TommyStyrvoky/Realm-card/animations/blizzard/1.bmp

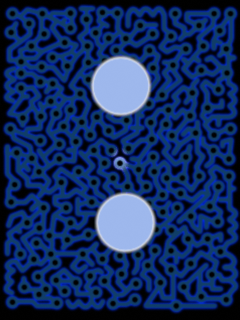
animations/blizzard/1.bmp
