TommyStyrvoky/Realm-card/animations/blizzard/3.bmp

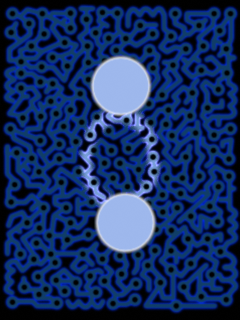
animations/blizzard/3.bmp
