TommyStyrvoky/Realm-card/animations/blizzard/4.bmp

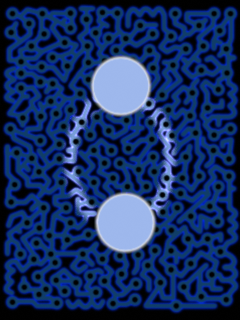
animations/blizzard/4.bmp
