TommyStyrvoky/Realm-card/animations/blizzard/6.bmp

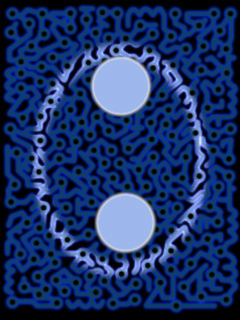
animations/blizzard/6.bmp
