TommyStyrvoky/Realm-card/animations/blizzard/7.bmp

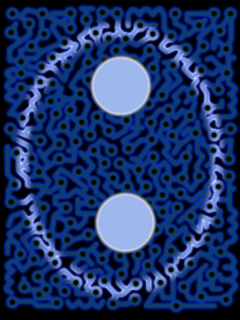
animations/blizzard/7.bmp
