TommyStyrvoky/Realm-card/animations/blizzard/8.bmp

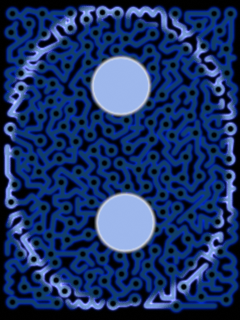
animations/blizzard/8.bmp
