TommyStyrvoky/Realm-card/animations/blizzard/9.bmp

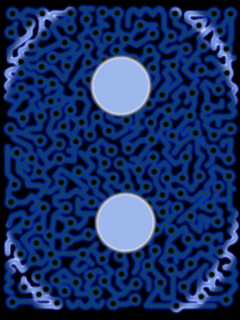
animations/blizzard/9.bmp
