TommyStyrvoky/Realm-card/animations/blizzard/10.bmp

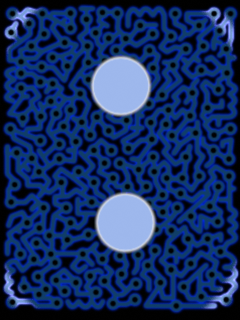
animations/blizzard/10.bmp
