TommyStyrvoky/Realm-card/animations/canyon/2.bmp

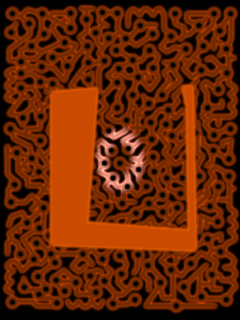
animations/canyon/2.bmp
