TommyStyrvoky/Realm-card/animations/canyon/3.bmp

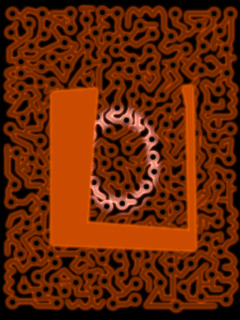
animations/canyon/3.bmp
