TommyStyrvoky/Realm-card/animations/canyon/4.bmp

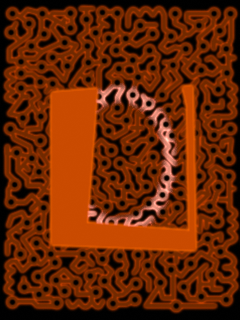
animations/canyon/4.bmp
