TommyStyrvoky/Realm-card/animations/canyon/5.bmp

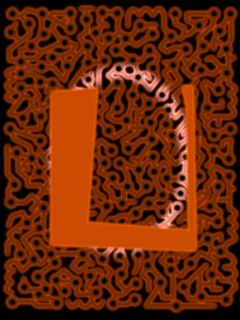
animations/canyon/5.bmp
