TommyStyrvoky/Realm-card/animations/canyon/6.bmp

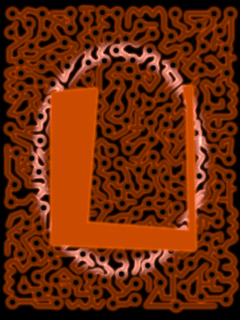
animations/canyon/6.bmp
