TommyStyrvoky/Realm-card/animations/canyon/7.bmp

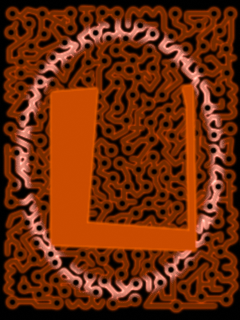
animations/canyon/7.bmp
