TommyStyrvoky/Realm-card/animations/canyon/8.bmp

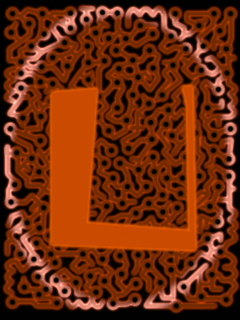
animations/canyon/8.bmp
