TommyStyrvoky/Realm-card/animations/canyon/9.bmp

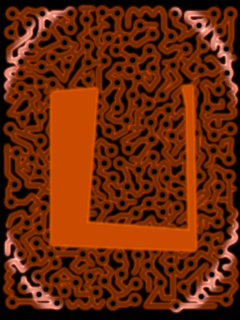
animations/canyon/9.bmp
