TommyStyrvoky/Realm-card/animations/canyon/10.bmp

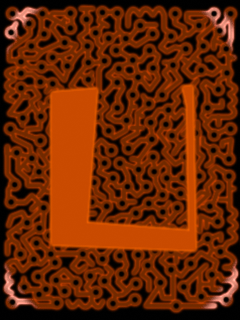
animations/canyon/10.bmp
