TommyStyrvoky/Realm-card/animations/cavern/1.bmp

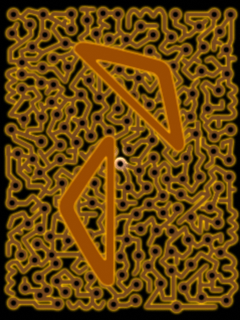
animations/cavern/1.bmp
