TommyStyrvoky/Realm-card/animations/cavern/3.bmp

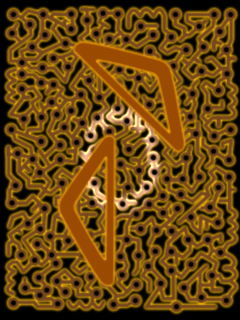
animations/cavern/3.bmp
