TommyStyrvoky/Realm-card/animations/cavern/5.bmp

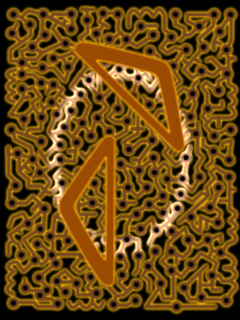
animations/cavern/5.bmp
