TommyStyrvoky/Realm-card/animations/cavern/6.bmp

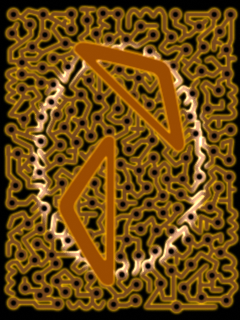
animations/cavern/6.bmp
