TommyStyrvoky/Realm-card/animations/cavern/7.bmp

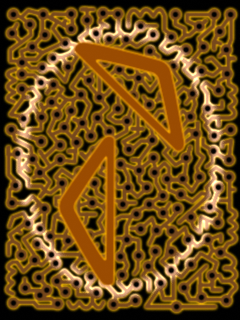
animations/cavern/7.bmp
