TommyStyrvoky/Realm-card/animations/cavern/8.bmp

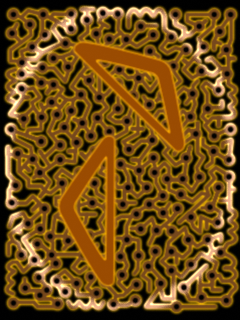
animations/cavern/8.bmp
