TommyStyrvoky/Realm-card/animations/cavern/9.bmp

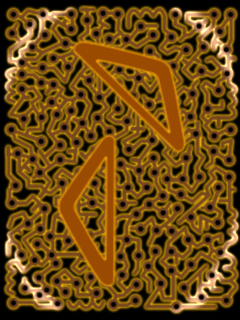
animations/cavern/9.bmp
