TommyStyrvoky/Realm-card/animations/cavern/10.bmp

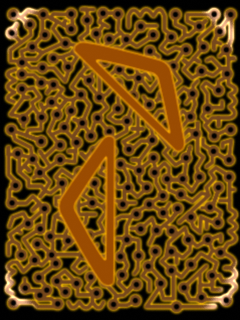
animations/cavern/10.bmp
