TommyStyrvoky/Realm-card/animations/chrome/1.bmp

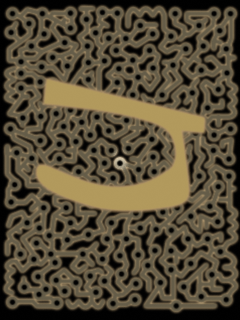
animations/chrome/1.bmp
