TommyStyrvoky/Realm-card/animations/chrome/3.bmp

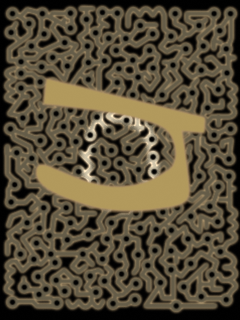
animations/chrome/3.bmp
