TommyStyrvoky/Realm-card/animations/chrome/5.bmp

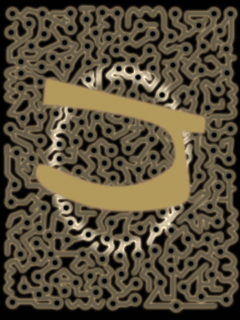
animations/chrome/5.bmp
