TommyStyrvoky/Realm-card/animations/chrome/7.bmp

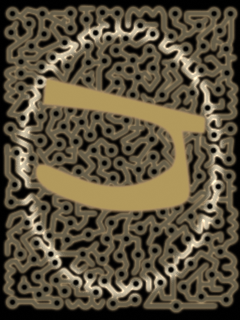
animations/chrome/7.bmp
