TommyStyrvoky/Realm-card/animations/chrome/8.bmp

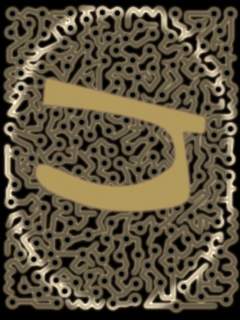
animations/chrome/8.bmp
