TommyStyrvoky/Realm-card/animations/chrome/9.bmp

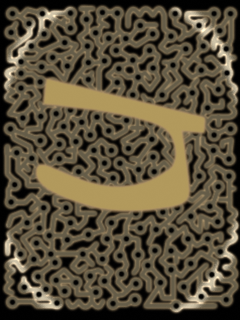
animations/chrome/9.bmp
