TommyStyrvoky/Realm-card/animations/chrome/10.bmp

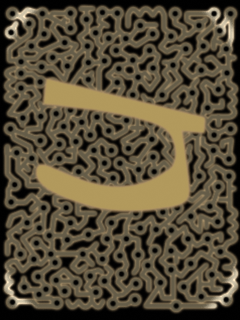
animations/chrome/10.bmp
