TommyStyrvoky/Realm-card/animations/cliffside/1.bmp

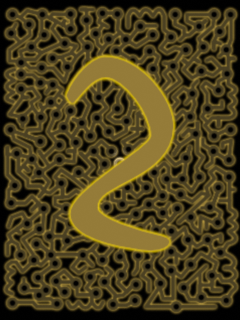
animations/cliffside/1.bmp
