TommyStyrvoky/Realm-card/animations/cliffside/5.bmp

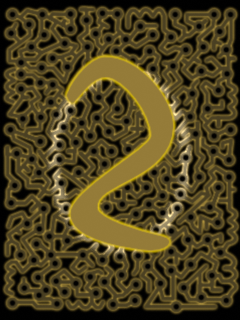
animations/cliffside/5.bmp
