TommyStyrvoky/Realm-card/animations/cliffside/6.bmp

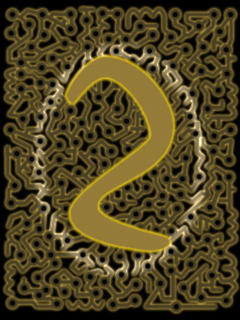
animations/cliffside/6.bmp
