TommyStyrvoky/Realm-card/animations/cliffside/7.bmp

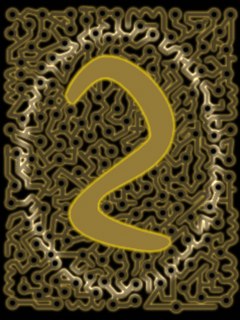
animations/cliffside/7.bmp
