TommyStyrvoky/Realm-card/animations/cosmic/3.bmp

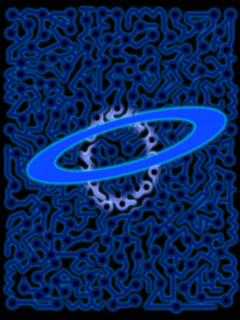
animations/cosmic/3.bmp
