TommyStyrvoky/Realm-card/animations/cosmic/5.bmp

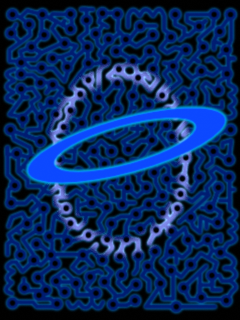
animations/cosmic/5.bmp
