TommyStyrvoky/Realm-card/animations/cosmic/6.bmp

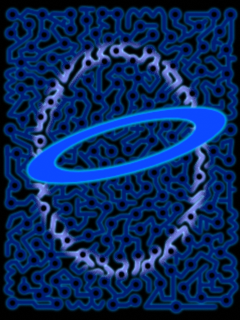
animations/cosmic/6.bmp
