TommyStyrvoky/Realm-card/animations/cosmic/7.bmp

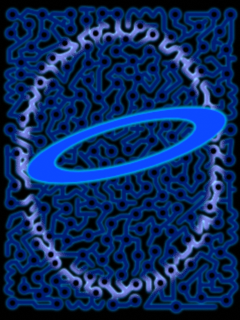
animations/cosmic/7.bmp
