TommyStyrvoky/Realm-card/animations/cosmic/8.bmp

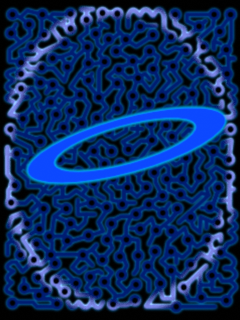
animations/cosmic/8.bmp
