TommyStyrvoky/Realm-card/animations/cosmic/9.bmp

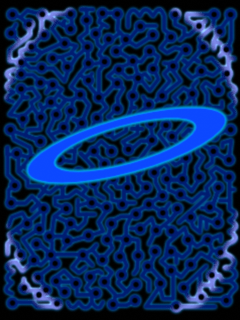
animations/cosmic/9.bmp
