TommyStyrvoky/Realm-card/animations/cybergrid/1.bmp

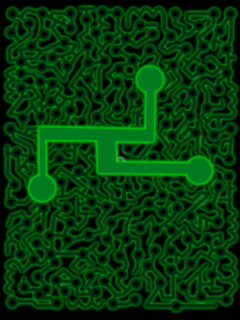
animations/cybergrid/1.bmp
