TommyStyrvoky/Realm-card/animations/cybergrid/4.bmp

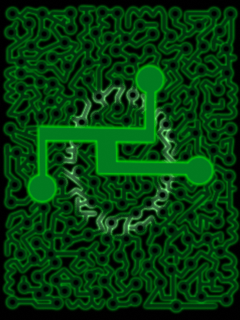
animations/cybergrid/4.bmp
