TommyStyrvoky/Realm-card/animations/cybergrid/5.bmp

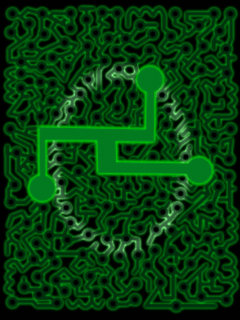
animations/cybergrid/5.bmp
