TommyStyrvoky/Realm-card/animations/cybergrid/6.bmp

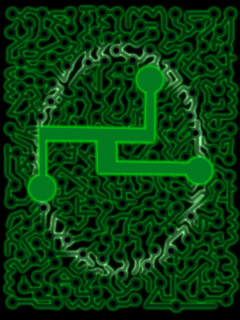
animations/cybergrid/6.bmp
