TommyStyrvoky/Realm-card/animations/cybergrid/7.bmp

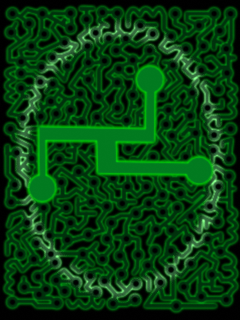
animations/cybergrid/7.bmp
