TommyStyrvoky/Realm-card/animations/cybergrid/8.bmp

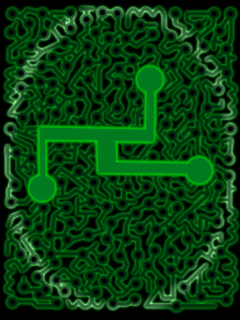
animations/cybergrid/8.bmp
