TommyStyrvoky/Realm-card/animations/cybergrid/9.bmp

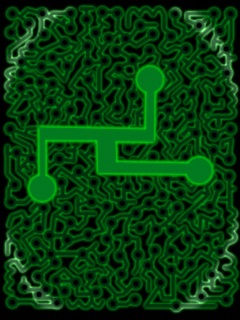
animations/cybergrid/9.bmp
