TommyStyrvoky/Realm-card/animations/cybergrid/10.bmp

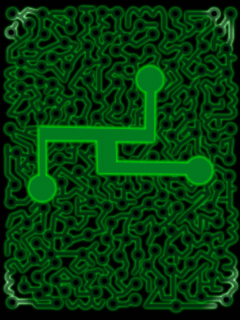
animations/cybergrid/10.bmp
