TommyStyrvoky/Realm-card/animations/desert/2.bmp

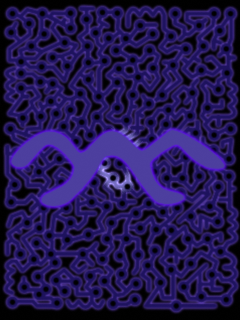
animations/desert/2.bmp
