TommyStyrvoky/Realm-card/animations/desert/4.bmp

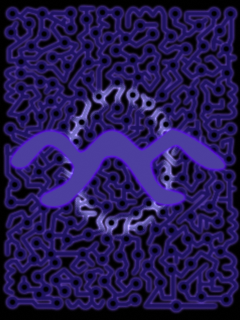
animations/desert/4.bmp
