TommyStyrvoky/Realm-card/animations/desert/5.bmp

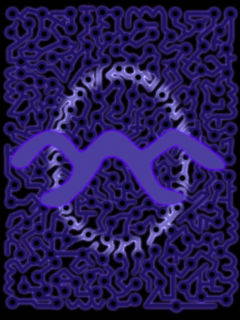
animations/desert/5.bmp
