TommyStyrvoky/Realm-card/animations/desert/7.bmp

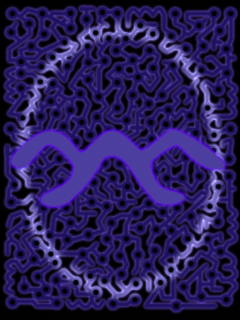
animations/desert/7.bmp
