TommyStyrvoky/Realm-card/animations/desert/8.bmp

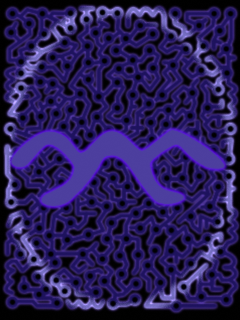
animations/desert/8.bmp
