TommyStyrvoky/Realm-card/animations/desert/9.bmp

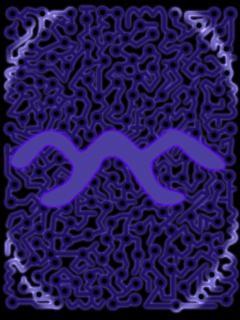
animations/desert/9.bmp
