TommyStyrvoky/Realm-card/animations/desert/10.bmp

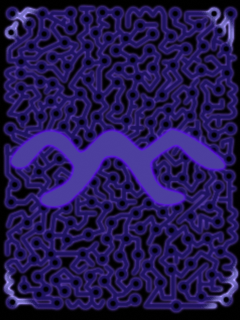
animations/desert/10.bmp
