TommyStyrvoky/Realm-card/animations/fog/1.bmp

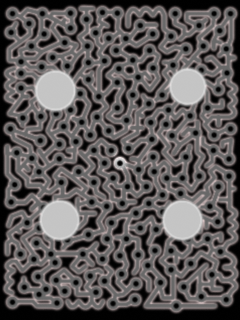
animations/fog/1.bmp
