TommyStyrvoky/Realm-card/animations/fog/3.bmp

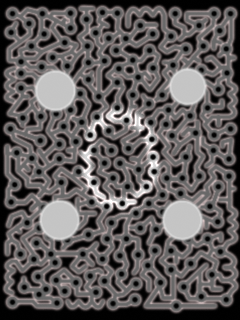
animations/fog/3.bmp
