TommyStyrvoky/Realm-card/animations/fog/4.bmp

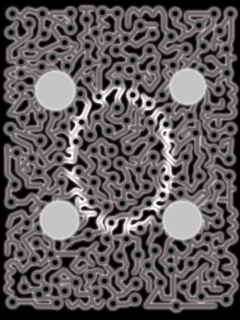
animations/fog/4.bmp
