TommyStyrvoky/Realm-card/animations/fog/5.bmp

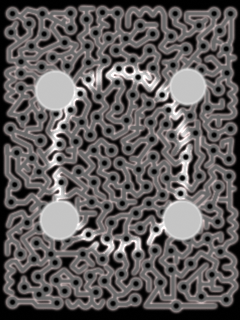
animations/fog/5.bmp
