TommyStyrvoky/Realm-card/animations/fog/6.bmp

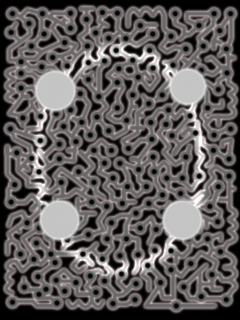
animations/fog/6.bmp
