TommyStyrvoky/Realm-card/animations/fog/7.bmp

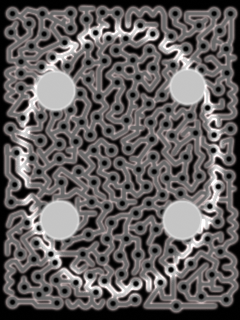
animations/fog/7.bmp
