TommyStyrvoky/Realm-card/animations/fog/8.bmp

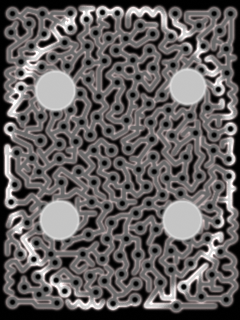
animations/fog/8.bmp
