TommyStyrvoky/Realm-card/animations/fog/9.bmp

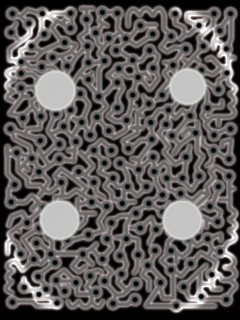
animations/fog/9.bmp
