TommyStyrvoky/Realm-card/animations/fog/10.bmp

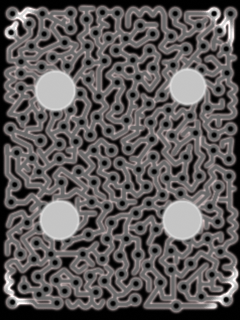
animations/fog/10.bmp
