TommyStyrvoky/Realm-card/animations/forest/1.bmp

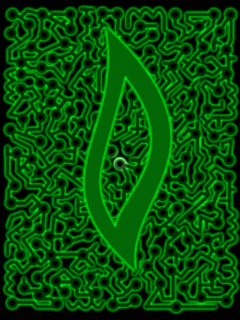
animations/forest/1.bmp
