TommyStyrvoky/Realm-card/animations/forest/4.bmp

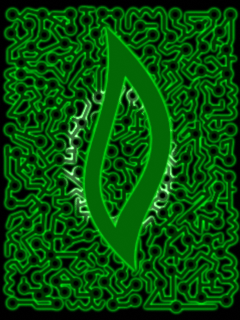
animations/forest/4.bmp
