TommyStyrvoky/Realm-card/animations/forest/6.bmp

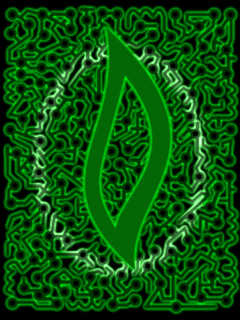
animations/forest/6.bmp
