TommyStyrvoky/Realm-card/animations/forest/7.bmp

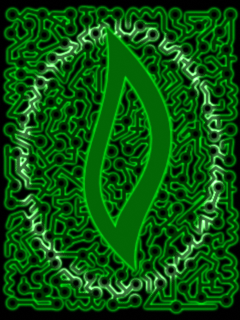
animations/forest/7.bmp
