TommyStyrvoky/Realm-card/animations/forest/8.bmp

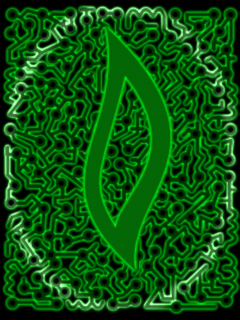
animations/forest/8.bmp
