TommyStyrvoky/Realm-card/animations/forest/9.bmp

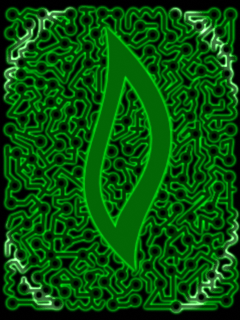
animations/forest/9.bmp
