TommyStyrvoky/Realm-card/animations/glass/2.bmp

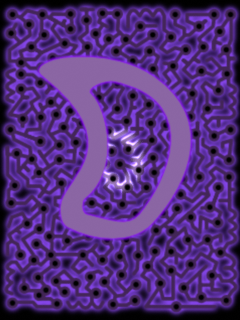
animations/glass/2.bmp
