TommyStyrvoky/Realm-card/animations/glass/3.bmp

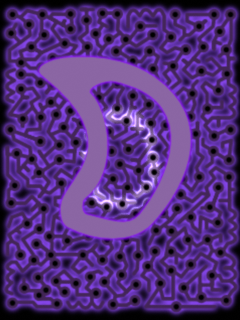
animations/glass/3.bmp
