TommyStyrvoky/Realm-card/animations/glass/4.bmp

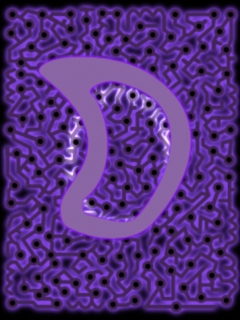
animations/glass/4.bmp
