TommyStyrvoky/Realm-card/animations/glass/5.bmp

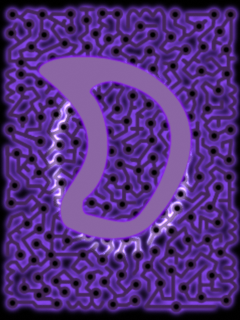
animations/glass/5.bmp
