TommyStyrvoky/Realm-card/animations/glass/6.bmp

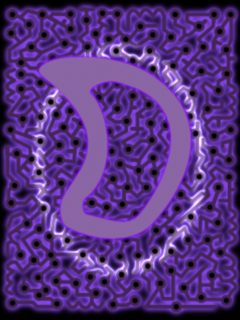
animations/glass/6.bmp
