TommyStyrvoky/Realm-card/animations/glass/7.bmp

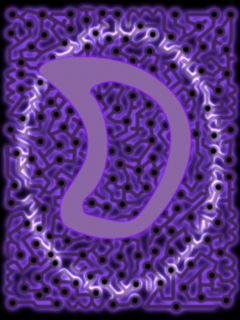
animations/glass/7.bmp
