TommyStyrvoky/Realm-card/animations/glass/8.bmp

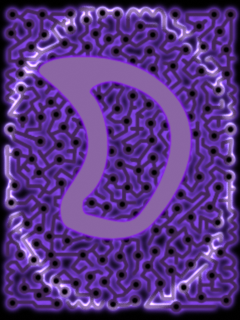
animations/glass/8.bmp
