TommyStyrvoky/Realm-card/animations/glass/9.bmp

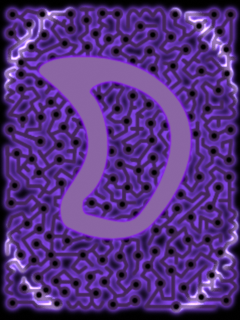
animations/glass/9.bmp
