TommyStyrvoky/Realm-card/animations/glass/10.bmp

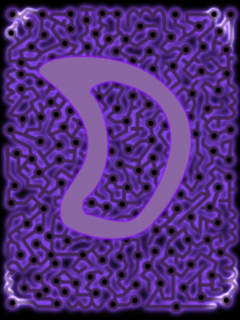
animations/glass/10.bmp
