TommyStyrvoky/Realm-card/animations/ice/1.bmp

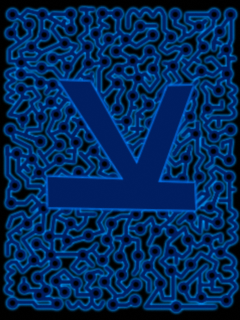
animations/ice/1.bmp
