TommyStyrvoky/Realm-card/animations/ice/3.bmp

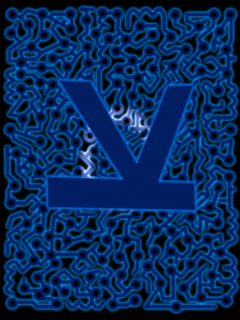
animations/ice/3.bmp
