TommyStyrvoky/Realm-card/animations/ice/4.bmp

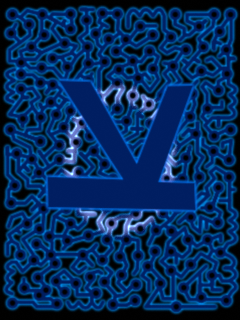
animations/ice/4.bmp
