TommyStyrvoky/Realm-card/animations/ice/5.bmp

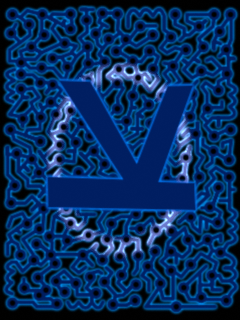
animations/ice/5.bmp
