TommyStyrvoky/Realm-card/animations/ice/8.bmp

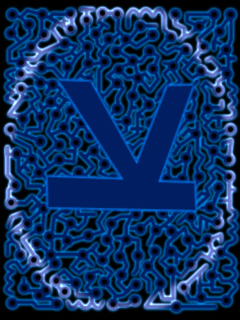
animations/ice/8.bmp
