TommyStyrvoky/Realm-card/animations/ice/9.bmp

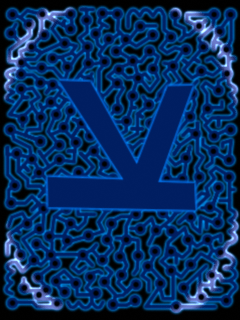
animations/ice/9.bmp
