TommyStyrvoky/Realm-card/animations/ice/10.bmp

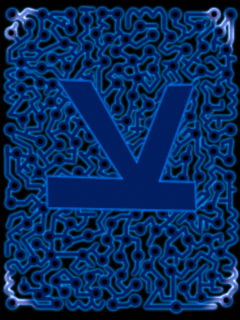
animations/ice/10.bmp
