TommyStyrvoky/Realm-card/animations/junk/1.bmp

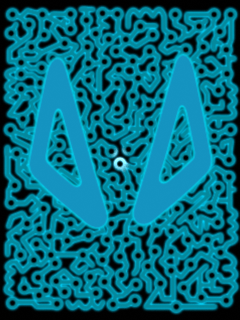
animations/junk/1.bmp
