TommyStyrvoky/Realm-card/animations/junk/2.bmp

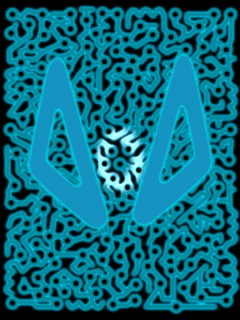
animations/junk/2.bmp
