TommyStyrvoky/Realm-card/animations/junk/3.bmp

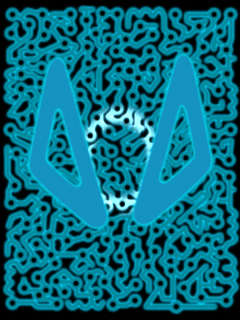
animations/junk/3.bmp
