TommyStyrvoky/Realm-card/animations/junk/6.bmp

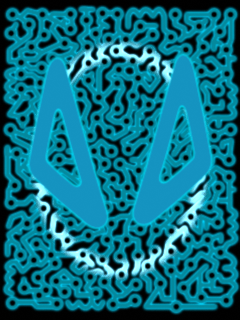
animations/junk/6.bmp
