TommyStyrvoky/Realm-card/animations/junk/7.bmp

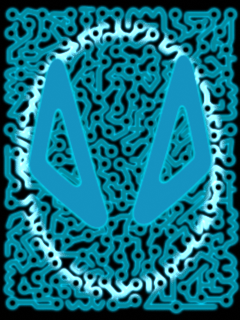
animations/junk/7.bmp
