TommyStyrvoky/Realm-card/animations/junk/8.bmp

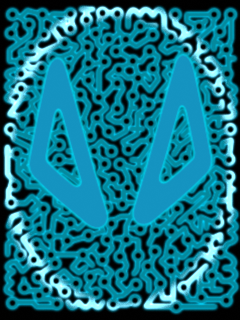
animations/junk/8.bmp
