TommyStyrvoky/Realm-card/animations/junk/9.bmp

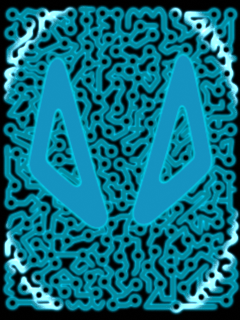
animations/junk/9.bmp
