TommyStyrvoky/Realm-card/animations/junk/10.bmp

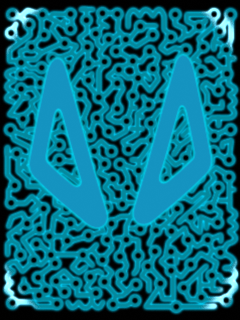
animations/junk/10.bmp
