TommyStyrvoky/Realm-card/animations/labyrinth/1.bmp

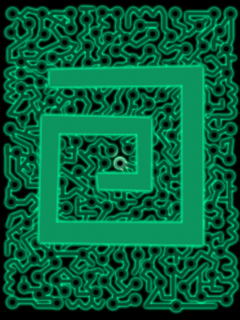
animations/labyrinth/1.bmp
