TommyStyrvoky/Realm-card/animations/labyrinth/3.bmp

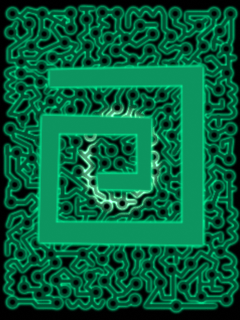
animations/labyrinth/3.bmp
