TommyStyrvoky/Realm-card/animations/labyrinth/4.bmp

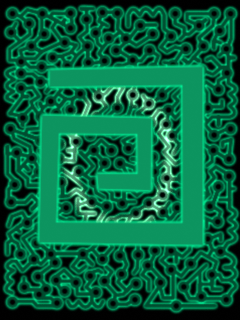
animations/labyrinth/4.bmp
