TommyStyrvoky/Realm-card/animations/labyrinth/6.bmp

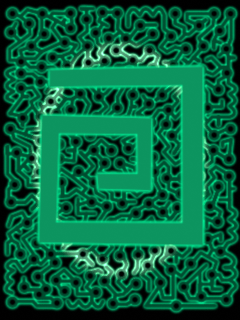
animations/labyrinth/6.bmp
