TommyStyrvoky/Realm-card/animations/labyrinth/7.bmp

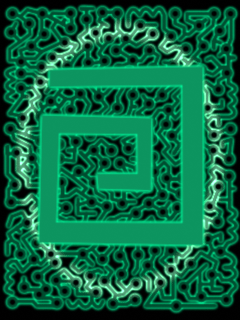
animations/labyrinth/7.bmp
