TommyStyrvoky/Realm-card/animations/labyrinth/8.bmp

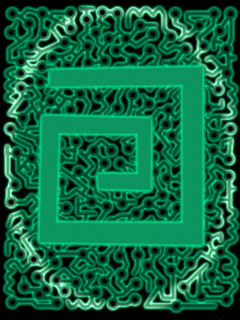
animations/labyrinth/8.bmp
