TommyStyrvoky/Realm-card/animations/labyrinth/9.bmp

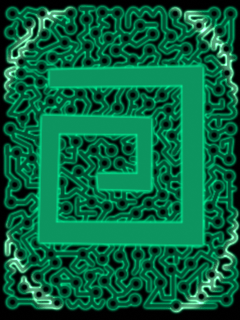
animations/labyrinth/9.bmp
