TommyStyrvoky/Realm-card/animations/labyrinth/10.bmp

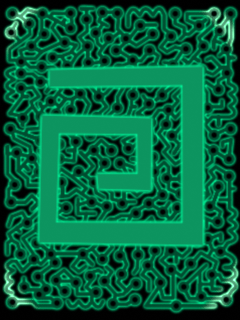
animations/labyrinth/10.bmp
