TommyStyrvoky/Realm-card/animations/lava/1.bmp

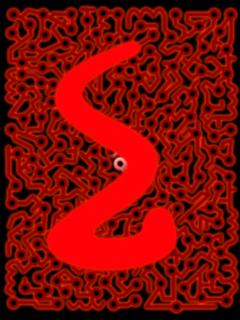
animations/lava/1.bmp
