TommyStyrvoky/Realm-card/animations/lava/3.bmp

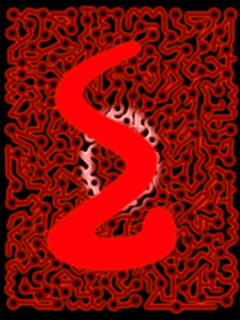
animations/lava/3.bmp
