TommyStyrvoky/Realm-card/animations/lava/5.bmp

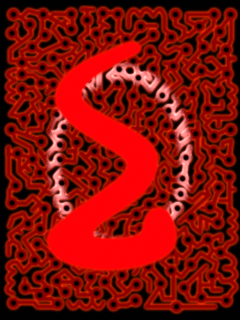
animations/lava/5.bmp
