TommyStyrvoky/Realm-card/animations/lava/6.bmp

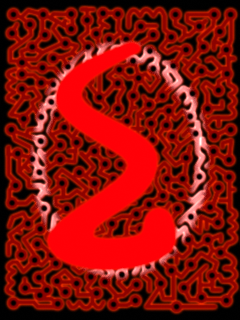
animations/lava/6.bmp
