TommyStyrvoky/Realm-card/animations/lava/7.bmp

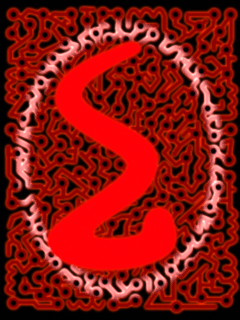
animations/lava/7.bmp
