TommyStyrvoky/Realm-card/animations/lava/8.bmp

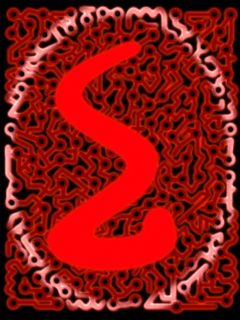
animations/lava/8.bmp
