TommyStyrvoky/Realm-card/animations/lava/9.bmp

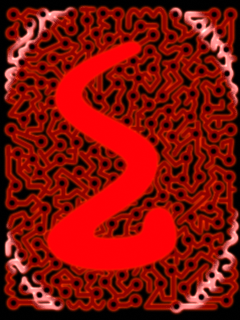
animations/lava/9.bmp
