TommyStyrvoky/Realm-card/animations/lava/10.bmp

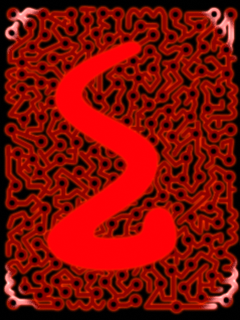
animations/lava/10.bmp
