TommyStyrvoky/Realm-card/animations/metro/1.bmp

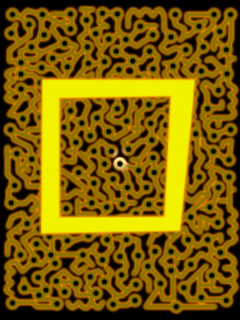
animations/metro/1.bmp
