TommyStyrvoky/Realm-card/animations/metro/3.bmp

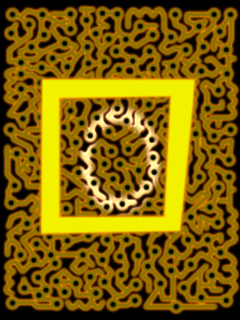
animations/metro/3.bmp
