TommyStyrvoky/Realm-card/animations/metro/4.bmp

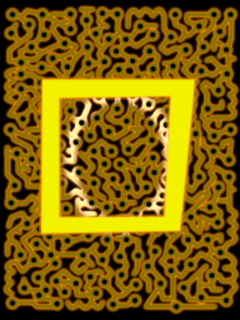
animations/metro/4.bmp
