TommyStyrvoky/Realm-card/animations/metro/5.bmp

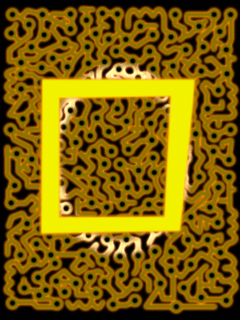
animations/metro/5.bmp
