TommyStyrvoky/Realm-card/animations/metro/7.bmp

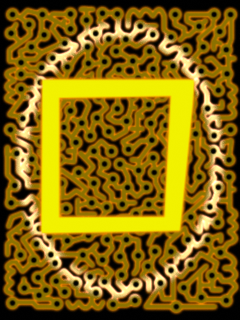
animations/metro/7.bmp
