TommyStyrvoky/Realm-card/animations/metro/8.bmp

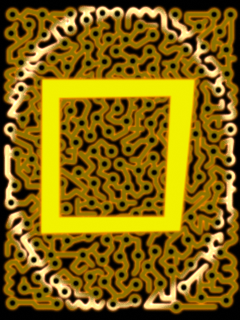
animations/metro/8.bmp
