TommyStyrvoky/Realm-card/animations/metro/9.bmp

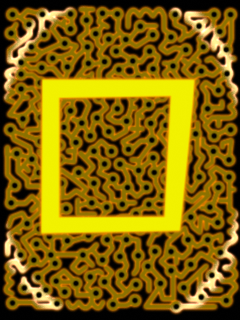
animations/metro/9.bmp
