TommyStyrvoky/Realm-card/animations/metro/10.bmp

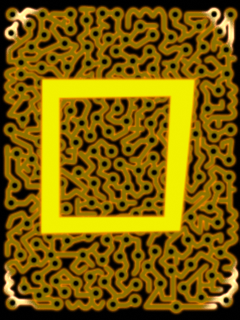
animations/metro/10.bmp
