TommyStyrvoky/Realm-card/animations/micro/1.bmp

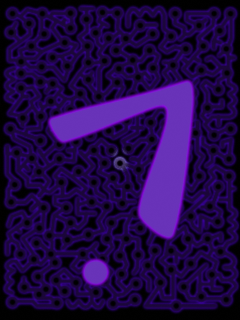
animations/micro/1.bmp
