TommyStyrvoky/Realm-card/animations/micro/3.bmp

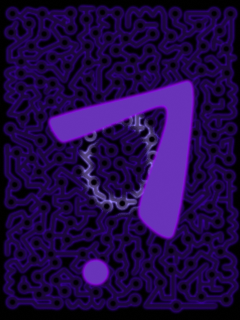
animations/micro/3.bmp
