TommyStyrvoky/Realm-card/animations/micro/4.bmp

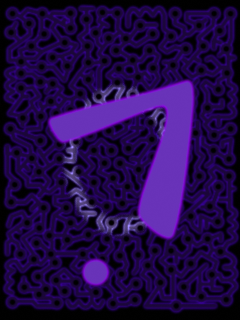
animations/micro/4.bmp
