TommyStyrvoky/Realm-card/animations/micro/6.bmp

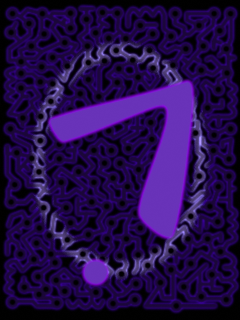
animations/micro/6.bmp
