TommyStyrvoky/Realm-card/animations/micro/7.bmp

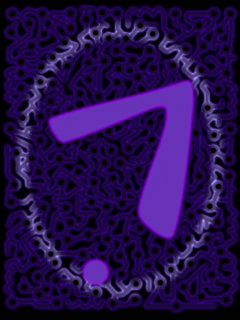
animations/micro/7.bmp
