TommyStyrvoky/Realm-card/animations/micro/8.bmp

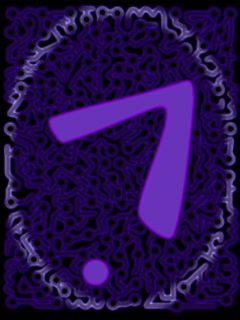
animations/micro/8.bmp
