TommyStyrvoky/Realm-card/animations/micro/9.bmp

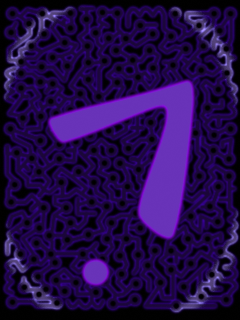
animations/micro/9.bmp
