TommyStyrvoky/Realm-card/animations/micro/10.bmp

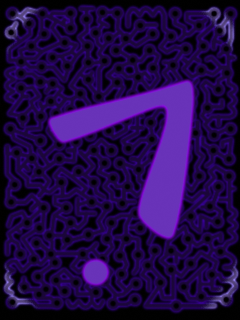
animations/micro/10.bmp
