TommyStyrvoky/Realm-card/animations/monument/1.bmp

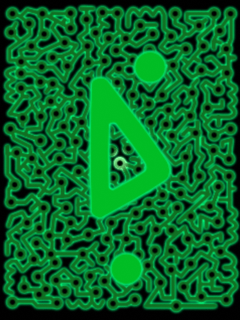
animations/monument/1.bmp
