TommyStyrvoky/Realm-card/animations/monument/4.bmp

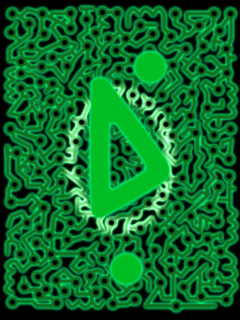
animations/monument/4.bmp
