TommyStyrvoky/Realm-card/animations/monument/6.bmp

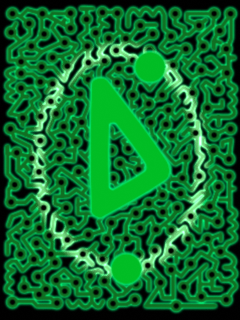
animations/monument/6.bmp
