TommyStyrvoky/Realm-card/animations/monument/7.bmp

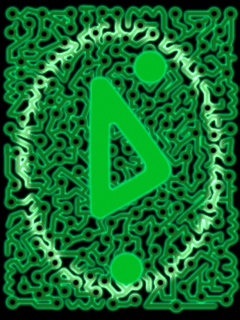
animations/monument/7.bmp
