TommyStyrvoky/Realm-card/animations/neon pipeline/1.bmp

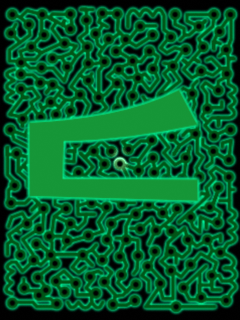
animations/neon pipeline/1.bmp
