TommyStyrvoky/Realm-card/animations/neon pipeline/2.bmp

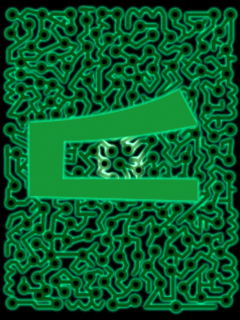
animations/neon pipeline/2.bmp
