TommyStyrvoky/Realm-card/animations/neon pipeline/4.bmp

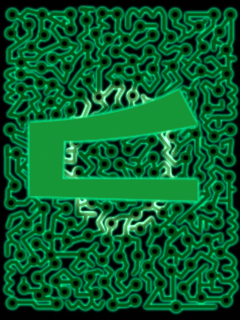
animations/neon pipeline/4.bmp
