TommyStyrvoky/Realm-card/animations/neon pipeline/6.bmp

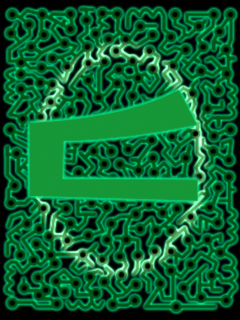
animations/neon pipeline/6.bmp
