TommyStyrvoky/Realm-card/animations/neon pipeline/7.bmp

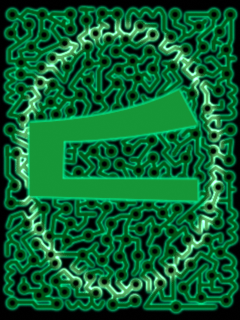
animations/neon pipeline/7.bmp
