TommyStyrvoky/Realm-card/animations/neon pipeline/8.bmp

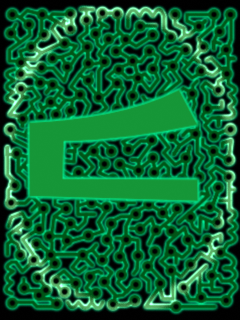
animations/neon pipeline/8.bmp
