TommyStyrvoky/Realm-card/animations/neon pipeline/9.bmp

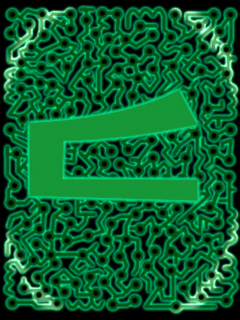
animations/neon pipeline/9.bmp
