TommyStyrvoky/Realm-card/animations/reactor/2.bmp

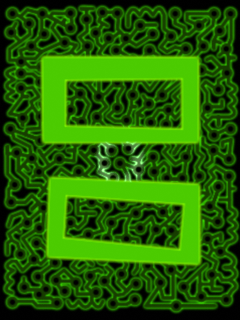
animations/reactor/2.bmp
