TommyStyrvoky/Realm-card/animations/reactor/5.bmp

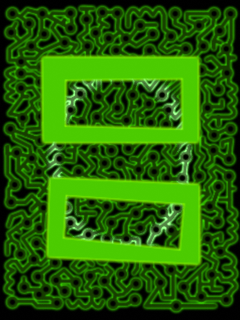
animations/reactor/5.bmp
