TommyStyrvoky/Realm-card/animations/reactor/6.bmp

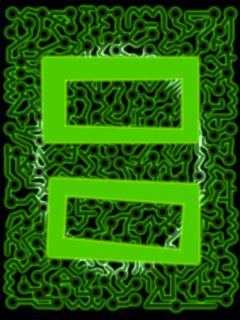
animations/reactor/6.bmp
