TommyStyrvoky/Realm-card/animations/reactor/7.bmp

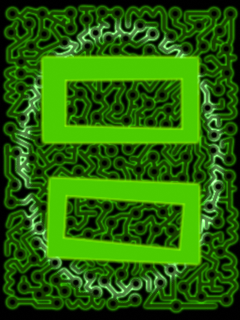
animations/reactor/7.bmp
