TommyStyrvoky/Realm-card/animations/reactor/8.bmp

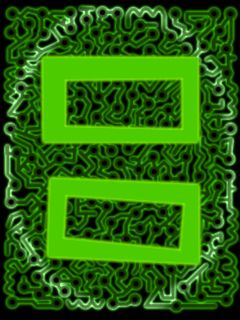
animations/reactor/8.bmp
