TommyStyrvoky/Realm-card/animations/reactor/10.bmp

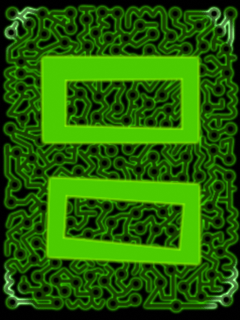
animations/reactor/10.bmp
