TommyStyrvoky/Realm-card/animations/ruins/1.bmp

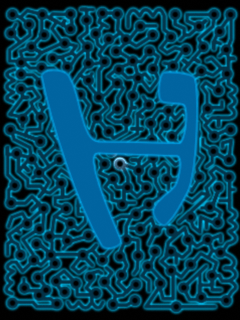
animations/ruins/1.bmp
