TommyStyrvoky/Realm-card/animations/ruins/3.bmp

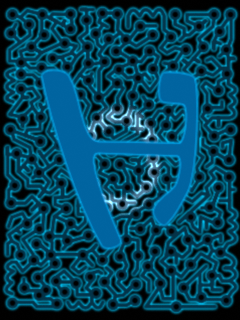
animations/ruins/3.bmp
