TommyStyrvoky/Realm-card/animations/ruins/4.bmp

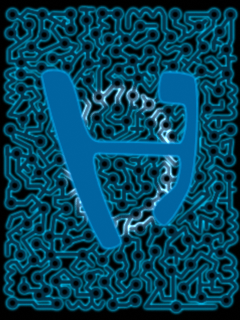
animations/ruins/4.bmp
