TommyStyrvoky/Realm-card/animations/ruins/7.bmp

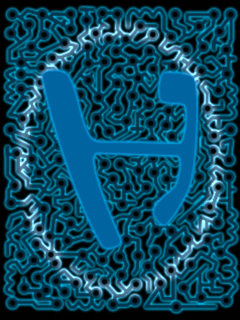
animations/ruins/7.bmp
