TommyStyrvoky/Realm-card/animations/ruins/10.bmp

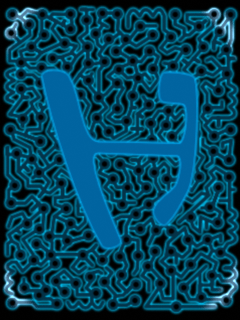
animations/ruins/10.bmp
