TommyStyrvoky/Realm-card/animations/sky/1.bmp

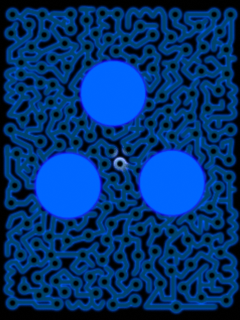
animations/sky/1.bmp
