TommyStyrvoky/Realm-card/animations/sky/3.bmp

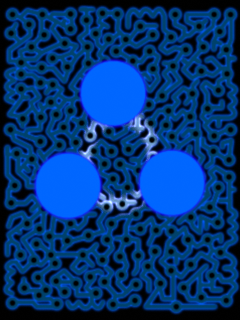
animations/sky/3.bmp
