TommyStyrvoky/Realm-card/animations/sky/4.bmp

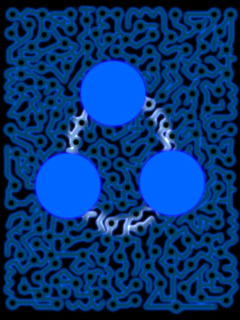
animations/sky/4.bmp
