TommyStyrvoky/Realm-card/animations/sky/5.bmp

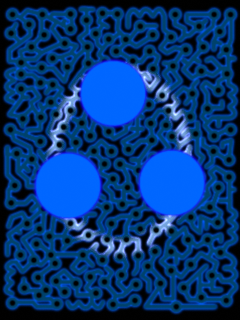
animations/sky/5.bmp
