TommyStyrvoky/Realm-card/animations/sky/6.bmp

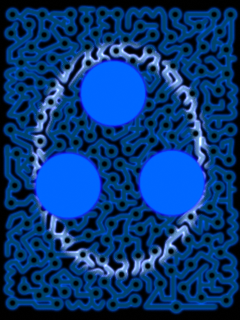
animations/sky/6.bmp
