TommyStyrvoky/Realm-card/animations/sky/7.bmp

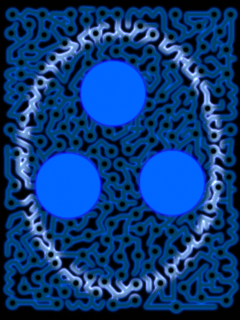
animations/sky/7.bmp
