TommyStyrvoky/Realm-card/animations/sky/8.bmp

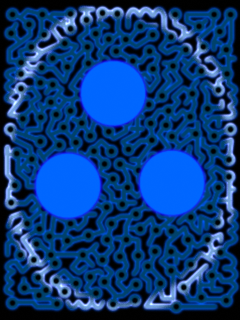
animations/sky/8.bmp
