TommyStyrvoky/Realm-card/animations/sky/9.bmp

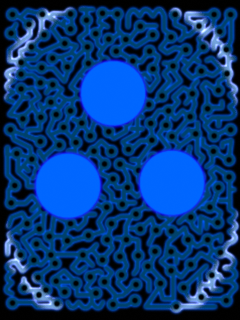
animations/sky/9.bmp
