TommyStyrvoky/Realm-card/animations/sky/10.bmp

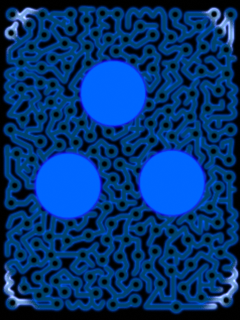
animations/sky/10.bmp
