TommyStyrvoky/Realm-card/animations/solar/1.bmp

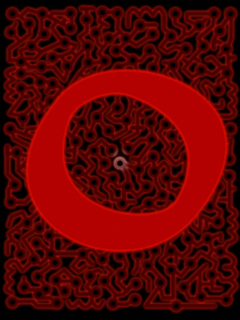
animations/solar/1.bmp
