TommyStyrvoky/Realm-card/animations/solar/3.bmp

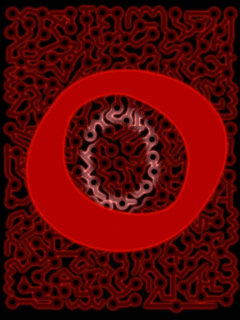
animations/solar/3.bmp
