TommyStyrvoky/Realm-card/animations/solar/4.bmp

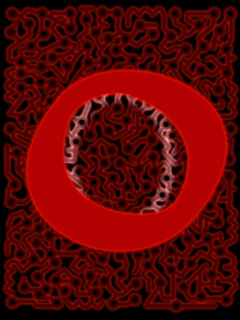
animations/solar/4.bmp
