TommyStyrvoky/Realm-card/animations/solar/5.bmp

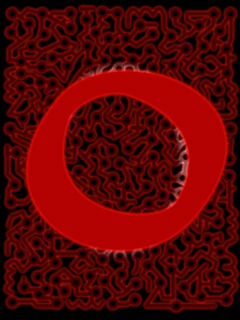
animations/solar/5.bmp
