TommyStyrvoky/Realm-card/animations/solar/7.bmp

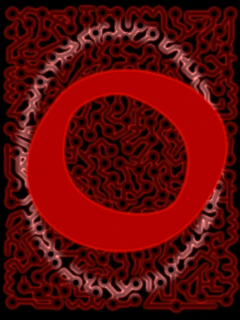
animations/solar/7.bmp
