TommyStyrvoky/Realm-card/animations/solar/8.bmp

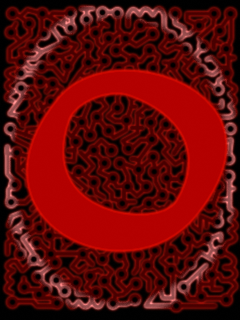
animations/solar/8.bmp
