TommyStyrvoky/Realm-card/animations/solar/10.bmp

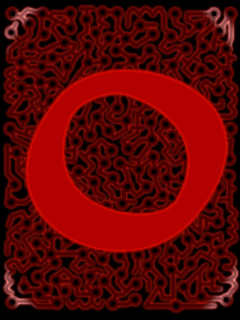
animations/solar/10.bmp
