TommyStyrvoky/Realm-card/animations/sound/1.bmp

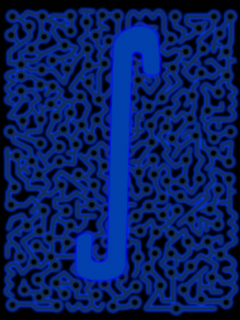
animations/sound/1.bmp
