TommyStyrvoky/Realm-card/animations/sound/3.bmp

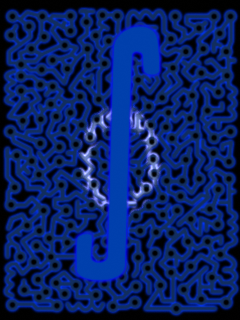
animations/sound/3.bmp
