TommyStyrvoky/Realm-card/animations/sound/4.bmp

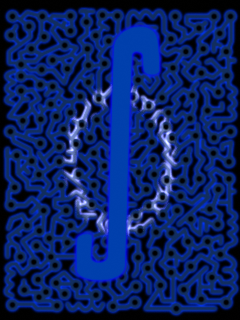
animations/sound/4.bmp
