TommyStyrvoky/Realm-card/animations/sound/5.bmp

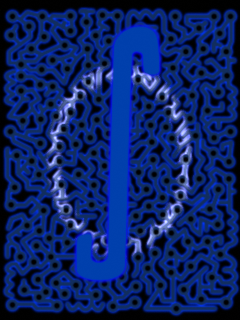
animations/sound/5.bmp
