TommyStyrvoky/Realm-card/animations/sound/6.bmp

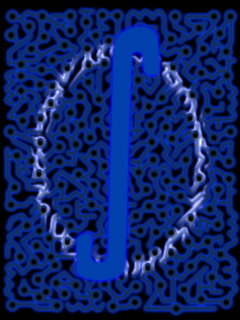
animations/sound/6.bmp
