TommyStyrvoky/Realm-card/animations/sound/7.bmp

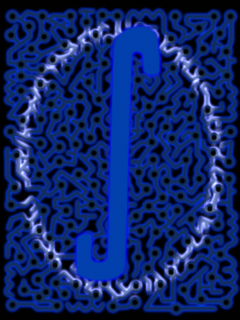
animations/sound/7.bmp
