TommyStyrvoky/Realm-card/animations/sound/8.bmp

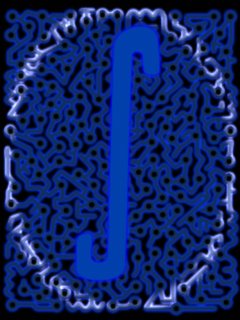
animations/sound/8.bmp
