TommyStyrvoky/Realm-card/animations/sound/9.bmp

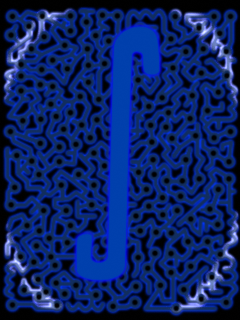
animations/sound/9.bmp
