TommyStyrvoky/Realm-card/animations/sound/10.bmp

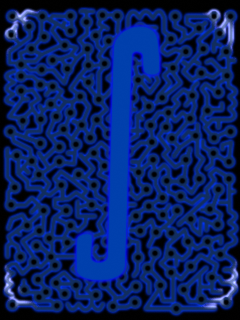
animations/sound/10.bmp
