TommyStyrvoky/Realm-card/animations/storm/1.bmp

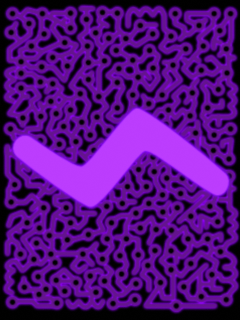
animations/storm/1.bmp
