TommyStyrvoky/Realm-card/animations/storm/4.bmp

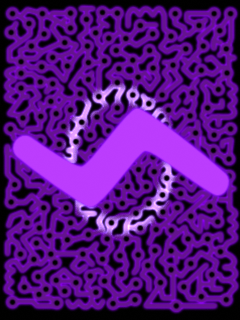
animations/storm/4.bmp
