TommyStyrvoky/Realm-card/animations/storm/5.bmp

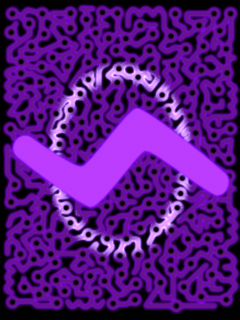
animations/storm/5.bmp
