TommyStyrvoky/Realm-card/animations/storm/6.bmp

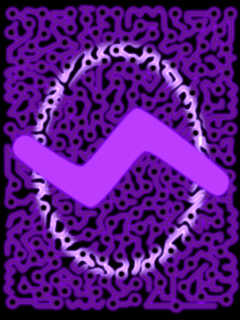
animations/storm/6.bmp
