TommyStyrvoky/Realm-card/animations/storm/7.bmp

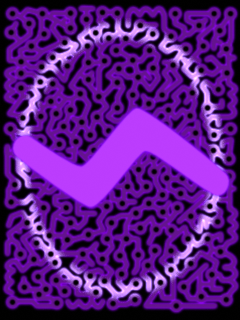
animations/storm/7.bmp
