TommyStyrvoky/Realm-card/animations/storm/8.bmp

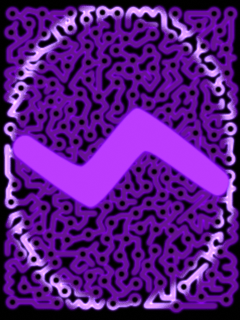
animations/storm/8.bmp
