TommyStyrvoky/Realm-card/animations/storm/10.bmp

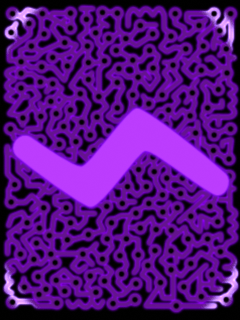
animations/storm/10.bmp
