TommyStyrvoky/Realm-card/animations/swamp/1.bmp

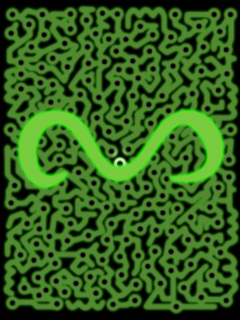
animations/swamp/1.bmp
