TommyStyrvoky/Realm-card/animations/swamp/3.bmp

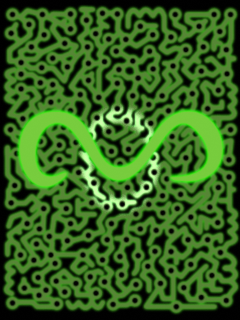
animations/swamp/3.bmp
