TommyStyrvoky/Realm-card/animations/swamp/4.bmp

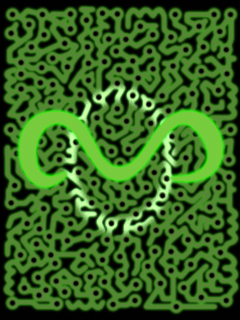
animations/swamp/4.bmp
