TommyStyrvoky/Realm-card/animations/swamp/7.bmp

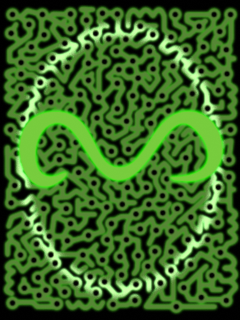
animations/swamp/7.bmp
