TommyStyrvoky/Realm-card/animations/swamp/8.bmp

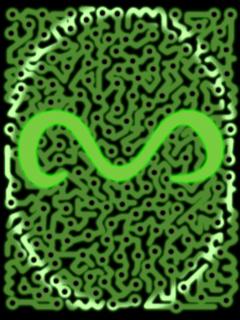
animations/swamp/8.bmp
