TommyStyrvoky/Realm-card/animations/swamp/9.bmp

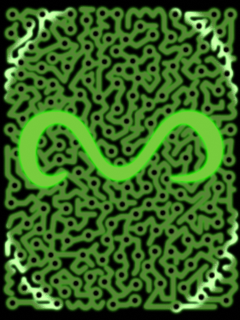
animations/swamp/9.bmp
