TommyStyrvoky/Realm-card/animations/warped/1.bmp

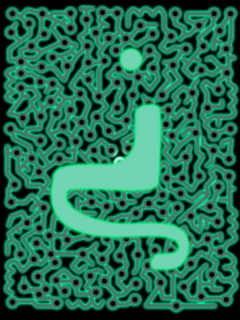
animations/warped/1.bmp
