TommyStyrvoky/Realm-card/animations/warped/3.bmp

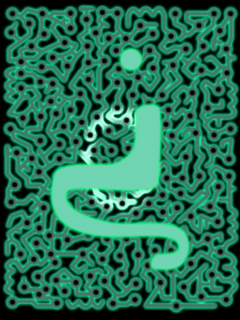
animations/warped/3.bmp
