TommyStyrvoky/Realm-card/animations/warped/4.bmp

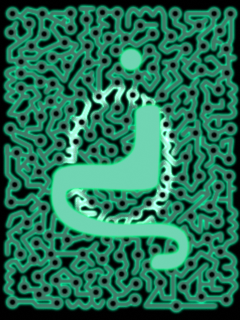
animations/warped/4.bmp
