TommyStyrvoky/Realm-card/animations/warped/6.bmp

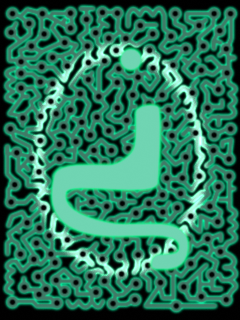
animations/warped/6.bmp
