TommyStyrvoky/Realm-card/animations/warped/7.bmp

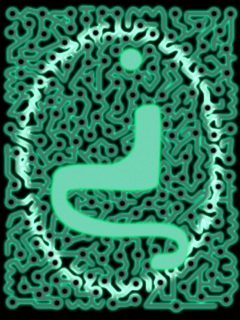
animations/warped/7.bmp
