TommyStyrvoky/Realm-card/animations/warped/9.bmp

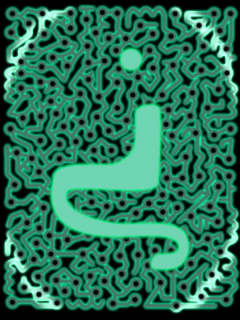
animations/warped/9.bmp
