TommyStyrvoky/Realm-card/animations/water/1.bmp

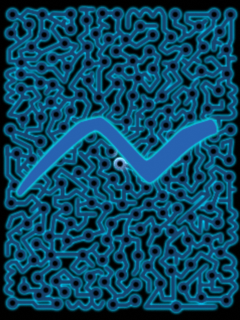
animations/water/1.bmp
