TommyStyrvoky/Realm-card/animations/water/3.bmp

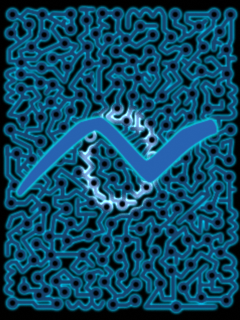
animations/water/3.bmp
