TommyStyrvoky/Realm-card/animations/water/4.bmp

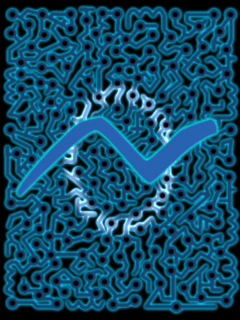
animations/water/4.bmp
