TommyStyrvoky/Realm-card/animations/water/6.bmp

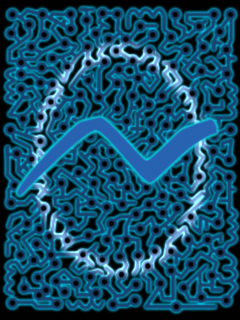
animations/water/6.bmp
