TommyStyrvoky/Realm-card/animations/water/7.bmp

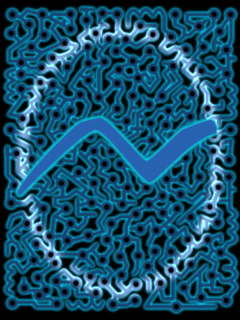
animations/water/7.bmp
