TommyStyrvoky/Realm-card/animations/water/9.bmp

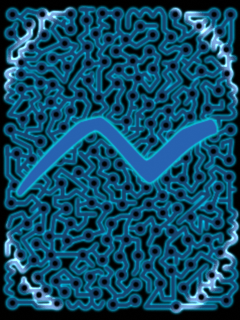
animations/water/9.bmp
