TommyStyrvoky/Realm-card/animations/water/10.bmp

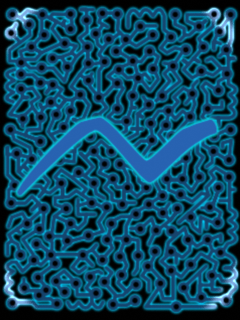
animations/water/10.bmp
