TommyStyrvoky/Realm-card/animations/wind/1.bmp

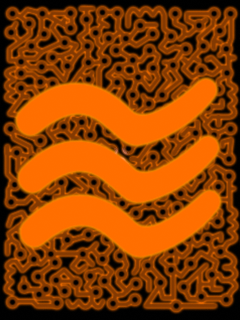
animations/wind/1.bmp
