TommyStyrvoky/Realm-card/animations/wind/4.bmp

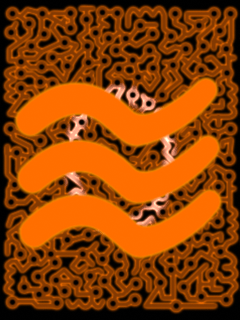
animations/wind/4.bmp
