TommyStyrvoky/Realm-card/animations/wind/5.bmp

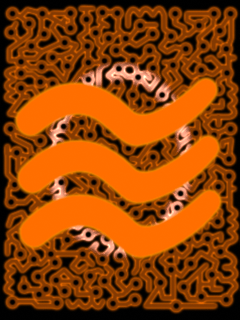
animations/wind/5.bmp
