TommyStyrvoky/Realm-card/animations/wind/6.bmp

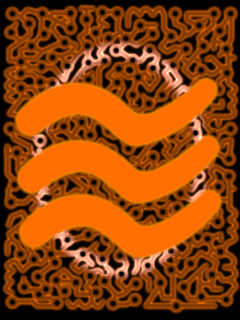
animations/wind/6.bmp
