TommyStyrvoky/Realm-card/animations/wind/7.bmp

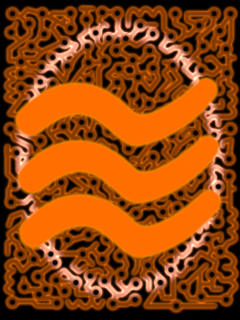
animations/wind/7.bmp
