TommyStyrvoky/Realm-card/animations/wind/8.bmp

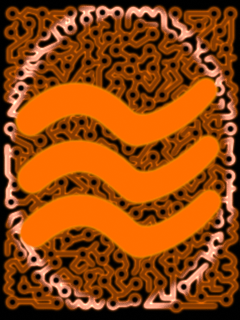
animations/wind/8.bmp
