TommyStyrvoky/Realm-card/animations/wind/9.bmp

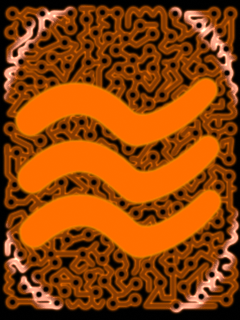
animations/wind/9.bmp
